sh123/esp32_loradv/variants/esp32dev_e22_sx1262/variant.h

#ifndef VARIANT_H
#define VARIANT_H

// e22 module type
#define USE_SX126X
#define MODULE_NAME                 SX1262      // 868 MHz module

// module specific ranges and base frequency
#define CFG_LORA_FREQ_RX            866.775e6   // RX frequency in MHz
#define CFG_LORA_FREQ_TX            866.775e6   // TX frequency in MHz
#define CFG_LORA_FREQ_MIN           850e6       // minimum frequency
#define CFG_LORA_FREQ_MAX           930e6       // maximum frequency

// LoRa pinougs
#define CFG_LORA_PIN_NSS            5
#define CFG_LORA_PIN_RST            26
#define CFG_LORA_PIN_DIO1           12          // (sx127x - dio0, sx126x/sx128x - dio1)
#define CFG_LORA_PIN_BUSY           14          // (sx127x - dio1, sx126x/sx128x - busy)
#define CFG_LORA_PIN_RXEN           32          // (sx127x - unused, sx126x - RXEN pin number)
#define CFG_LORA_PIN_TXEN           33          // (sx127x - unused, sx126x - TXEN pin number)

#endif // VARIANT_H
