sh123/esp32_loradv/include/loradv_config.h

#ifndef LORADV_CONFIG_H
#define LORADV_CONFIG_H

#include <Arduino.h>
#include <Preferences.h>
#include <DebugLog.h>

#include "version.h"

#if __has_include("/tmp/esp32_loradv_config.h")
#pragma message("Using external config")
#include "/tmp/esp32_loradv_config.h"
#else
#pragma message("Using default built-in config")
#include "config.h"
#endif

namespace LoraDv {

class Config {
public:
  int Version;          // config version

  DebugLogLevel LogLevel;    // log level

  // modulation type
  int ModType;          // 0 - lora, 1 - fsk

  // lora modulation parameters
  long LoraFreqRx;      // lora RX frequency, e.g. 433.775e6
  long LoraFreqTx;      // lora TX frequency, e.g. 433.775e6
  long LoraFreqStep;    // lora frequency step
  long LoraBw;          // lora bandwidth, e.g. 125e3
  int LoraSf;           // lora spreading factor, e.g. 12
  int LoraCodingRate;   // lora coding rate, e.g. 7
  int LoraPower;        // lora power level in dbm, 20
  int LoraSync_;        // lora sync word/packet id, 0x34
  int LoraCrc_;         // lora crc mode, 0 - disabled, 1 - 1 byte, 2 - 2 bytes
  int LoraPreambleLen_; // lora preamble length from 6 to 65535

  // fsk modulation parameters
  float FskBitRate;     // fsk bit rate, 0.6 - 300.0 Kbps
  float FskFreqDev;     // fsk frequency deviation 0.6 - 200 kHz
  float FskRxBw;        // fsk rx bandwidth, discrete from 4.8 to 467 kHz
  byte FskShaping;      // fsk gaussian shaping

  // lora hardware pinouts and isr
  byte LoraPinSs_;       // lora ss pin
  byte LoraPinRst_;      // lora rst pin
  byte LoraPinA_;        // (sx127x - dio0, sx126x/sx128x - dio1)
  byte LoraPinB_;        // (sx127x - dio1, sx126x/sx128x - busy)
  byte LoraPinSwitchRx_; // (sx127x - unused, sx126x - RXEN pin number)
  byte LoraPinSwitchTx_; // (sx127x - unused, sx126x - TXEN pin number)

  // rotary encoder
  byte EncoderPinA_;     // Encoder A pin number
  byte EncoderPinB_;     // Encoder B pin number
  byte EncoderPinBtn_;   // Encoder button pin number
  byte EncoderPinVcc_;   // Encoder VCC pin (or -1 if not connected)
  byte EncoderSteps_;    // Encoder number of steps

  // audio params
  int AudioCodec;         // type of audio codec, 0 - Codec2, 1 - OPUS
  int AudioResampleCoeff_; // resample coefficient when audio rate is not equal code rate
  uint32_t AudioSampleRate_; // sample rate for mic and speaker
  uint32_t AudioCodecSampleRate_; // sammple rate for codec
  int AudioHpfCutoffHz_;  // high pass fitler cutoff frequency

  // codec2
  int AudioCodec2Mode;   // Audio Codec2 mode
  int AudioMaxPktSize;   // Aggregated packet maximum size

  // audio opus
  int AudioOpusRate;  // opus bit rate 2.4 - 512 kbps
  float AudioOpusPcmLen;   // opus pcm frame length, 2.5, 5, 10, 20, 40, 60, 80, 100, 120 ms  

  // i2s speaker
  byte AudioSpkPinBclk_; // Speaker i2s clk pin
  byte AudioSpkPinLrc_;  // Speaker i2s lrc pin
  byte AudioSpkPinDin_;  // Speaker i2s din pin

  // i2s mic
  byte AudioMicPinSd_;   // Mic i2s sd pin
  byte AudioMicPinWs_;   // Mic i2s ws pin
  byte AudioMicPinSck_;  // Mic i2s sck pin

  // audio state
  int AudioMaxVol_;      // maximum volume
  int AudioVol;          // current volume

  // privacy
  bool AudioEnPriv;     // enable/disable privacy
  byte AudioPrivacyKey_[32]; // privacy key

  // battery monitor
  byte BatteryMonPin_;   // Battery monitor adc pin
  float BatteryMonCal;   // Battery monitor calibrarion value

  // power management
  int PmSleepAfterMs; // Light sleep activation after given ms
  int PmLightSleepDurationMs_; // How long to sleep
  int PmLightSleepAwakeMs_; // How long to be active

  // ptt button
  int PttBtnPin_;            // ptt pin

public:
  Config();
  void Load();
  void Save();
  void Reset();

private:
  void InitializeDefault();

  Preferences prefs_;

}; // Config

} // LoraDv

#endif // LORADV_CONFIG_H
