sh123/esp32_loradv/include/audio_codec_codec2.h

#ifndef AUDIO_CODEC2_H
#define AUDIO_CODEC2_H

#include "audio_codec.h"

namespace LoraDv {

class AudioCodecCodec2 : public AudioCodec {

public:
  AudioCodecCodec2();

  virtual bool start(std::shared_ptr<const Config> config) override;
  virtual void stop() override;

  virtual int encode(uint8_t *encodedOut, int16_t *pcmIn) override;
  virtual int decode(int16_t *pcmOut, uint8_t *encodedIn, uint16_t encodedSize) override;

  virtual bool isFixedFrameSize() const override { return true; }

  virtual int getFrameSize() const override;
  virtual int getPcmFrameSize() const override;
  virtual int getPcmFrameBufferSize() const override;

private:
  struct CODEC2 *codec_; 

  int codecSamplesPerFrame_;
  int codecBytesPerFrame_;
};

} // namespace LoraDv

#endif // AUDIO_CODEC2_H
