sh123/esp32_loradv/src/hw_monitor.cpp

#include "hw_monitor.h"

namespace LoraDv {

HwMonitor::HwMonitor() 
  : config_(nullptr)
{
}

void HwMonitor::setup(std::shared_ptr<const Config> config)
{
  config_ = config;
}

float HwMonitor::getBatteryVoltage() const
{
  int bat_value = analogRead(config_->BatteryMonPin_);
  return 2 * bat_value * (3.3 / 4096.0) + config_->BatteryMonCal;
}

} // LoraDv
